taejun20/QuadStretcher/QuadStretcher Unity/Assets/Downloaded Assets/Free medieval weapons/Textures/Arrows_Arrows_AlbedoTransparency.png

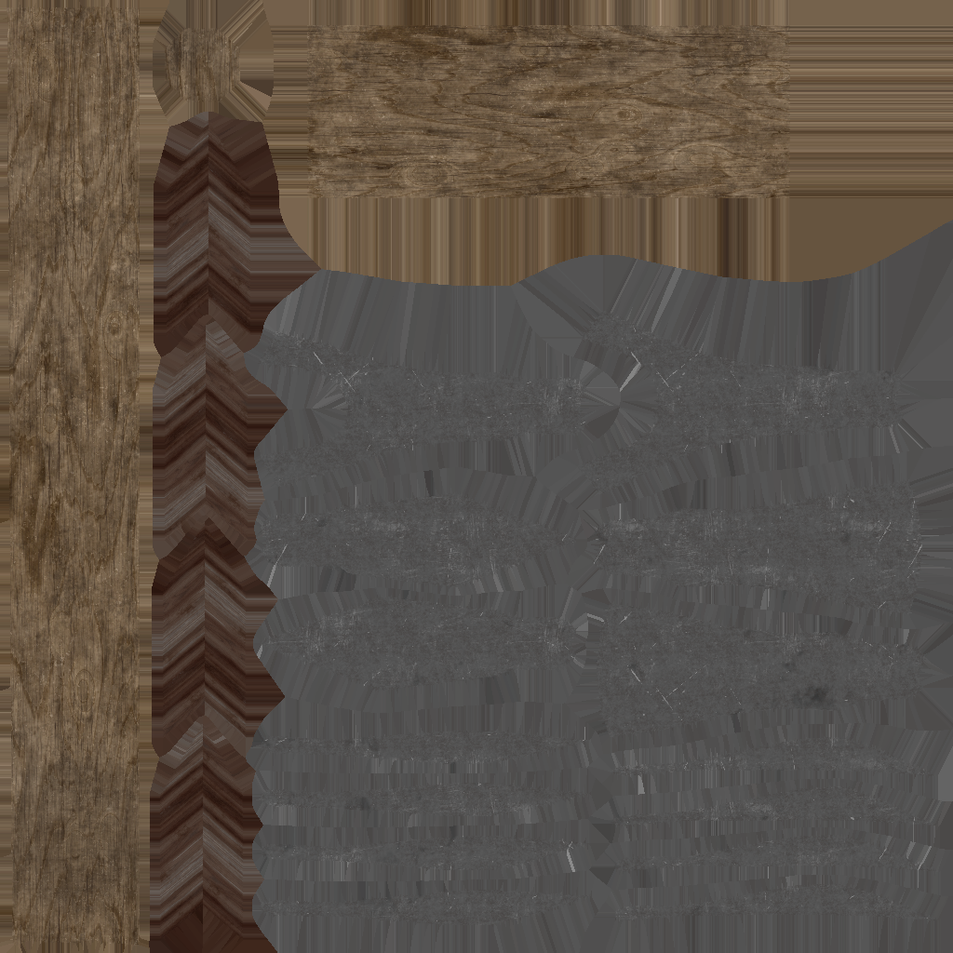
QuadStretcher Unity/Assets/Downloaded Assets/Free medieval weapons/Textures/Arrows_Arrows_AlbedoTransparency.png
