taejun20/QuadStretcher/QuadStretcher Unity/Assets/Downloaded Assets/Free medieval weapons/Textures/OneSided_Axes_low_Axes_OS_AO.png

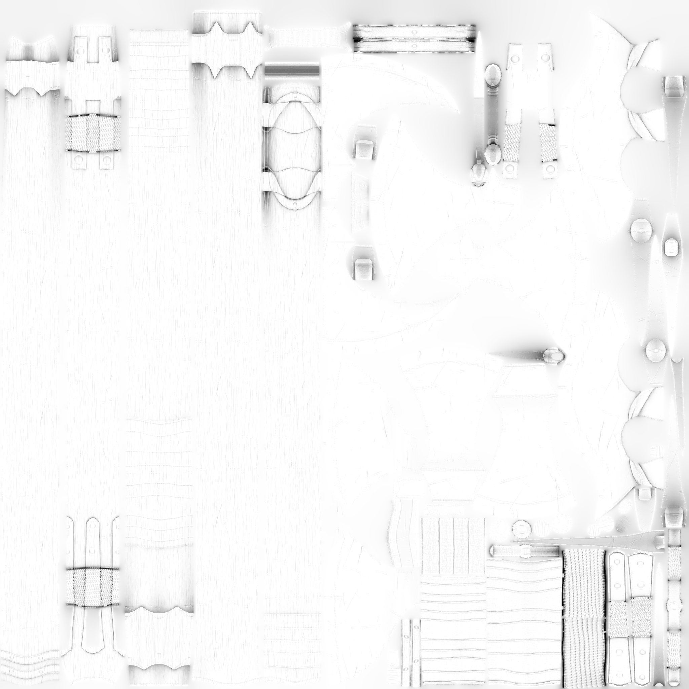
QuadStretcher Unity/Assets/Downloaded Assets/Free medieval weapons/Textures/OneSided_Axes_low_Axes_OS_AO.png
