taejun20/QuadStretcher/QuadStretcher Unity/Assets/Downloaded Assets/Free medieval weapons/Textures/Swords_low_Swords_OH_AO.png

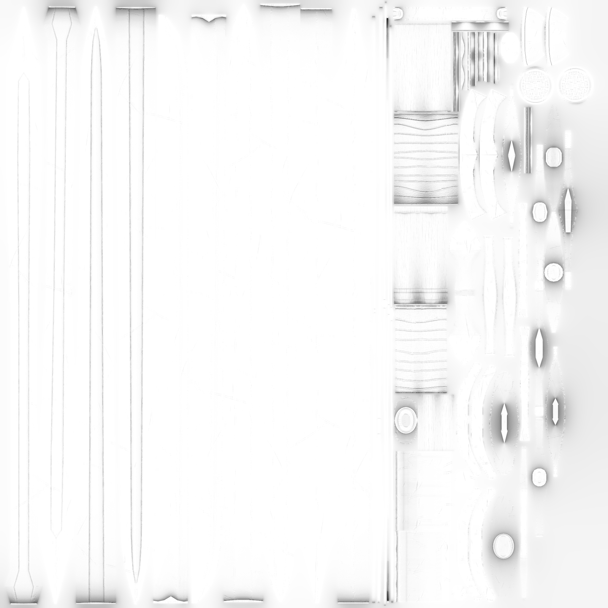
QuadStretcher Unity/Assets/Downloaded Assets/Free medieval weapons/Textures/Swords_low_Swords_OH_AO.png
