taejun20/QuadStretcher/QuadStretcher Unity/Assets/Downloaded Assets/Mega Fantasy Props Pack/Textures/bark_1_o.png

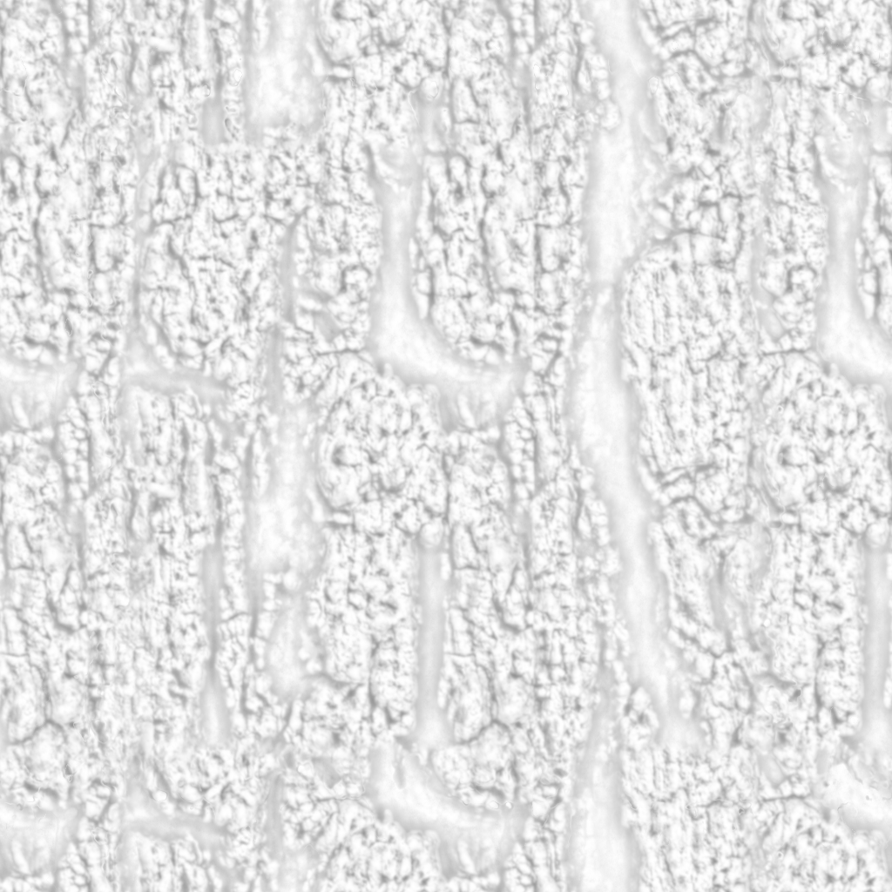
QuadStretcher Unity/Assets/Downloaded Assets/Mega Fantasy Props Pack/Textures/bark_1_o.png
