taejun20/QuadStretcher/QuadStretcher Unity/Assets/Downloaded Assets/Mega Fantasy Props Pack/Textures/books_paper_n.png

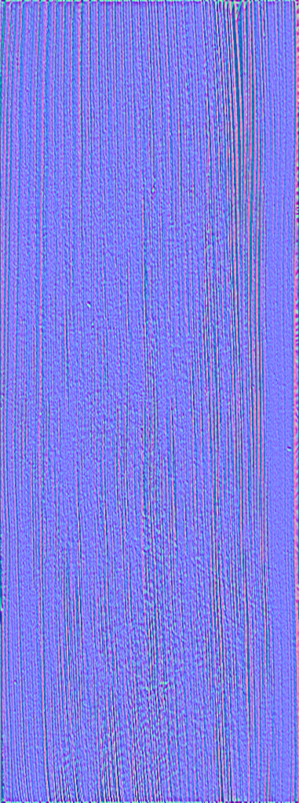
QuadStretcher Unity/Assets/Downloaded Assets/Mega Fantasy Props Pack/Textures/books_paper_n.png
