taejun20/QuadStretcher/QuadStretcher Unity/Assets/Downloaded Assets/Mega Fantasy Props Pack/Textures/books_paper_o.png

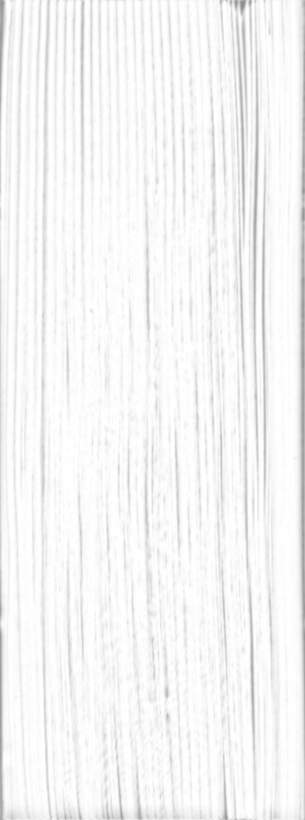
QuadStretcher Unity/Assets/Downloaded Assets/Mega Fantasy Props Pack/Textures/books_paper_o.png
