taejun20/QuadStretcher/QuadStretcher Unity/Assets/Downloaded Assets/Pistol 92/Textures/Pistol Bullet Metallic.png

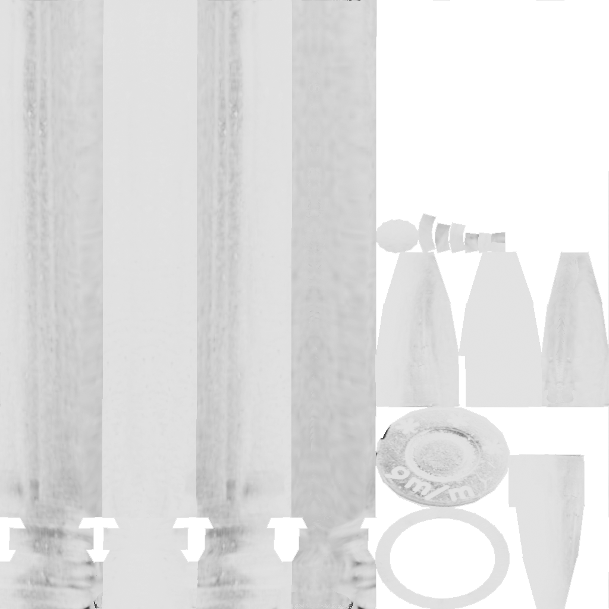
QuadStretcher Unity/Assets/Downloaded Assets/Pistol 92/Textures/Pistol Bullet Metallic.png
