taejun20/QuadStretcher/QuadStretcher Unity/Assets/Downloaded Assets/Pistol 92/Textures/Pistol Height.png

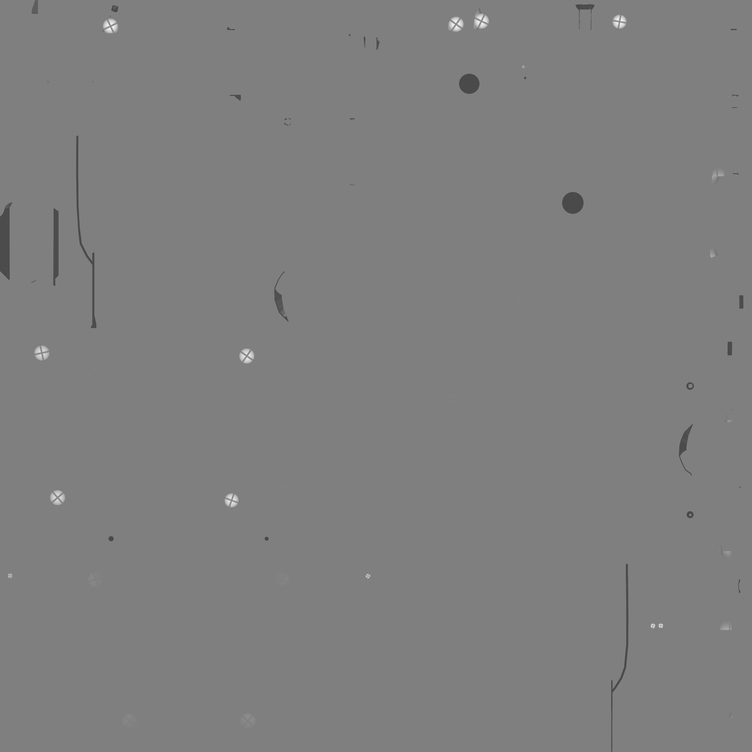
QuadStretcher Unity/Assets/Downloaded Assets/Pistol 92/Textures/Pistol Height.png
