taejun20/QuadStretcher/QuadStretcher Unity/Assets/Downloaded Assets/Platform_Pack/Pack_02_P/Texture/Folhagem_Pack_01__V2_Normal.png

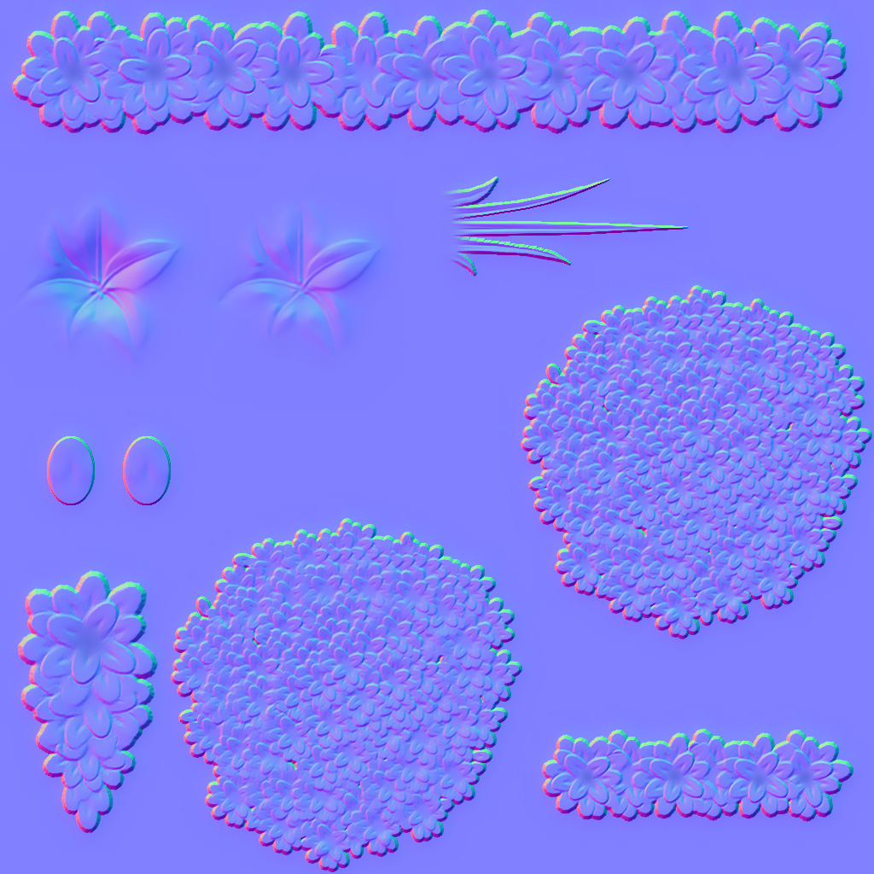
QuadStretcher Unity/Assets/Downloaded Assets/Platform_Pack/Pack_02_P/Texture/Folhagem_Pack_01__V2_Normal.png
