taejun20/QuadStretcher/QuadStretcher Unity/Assets/Downloaded Assets/Platform_Pack/S-EXTRA/Sky_01.png

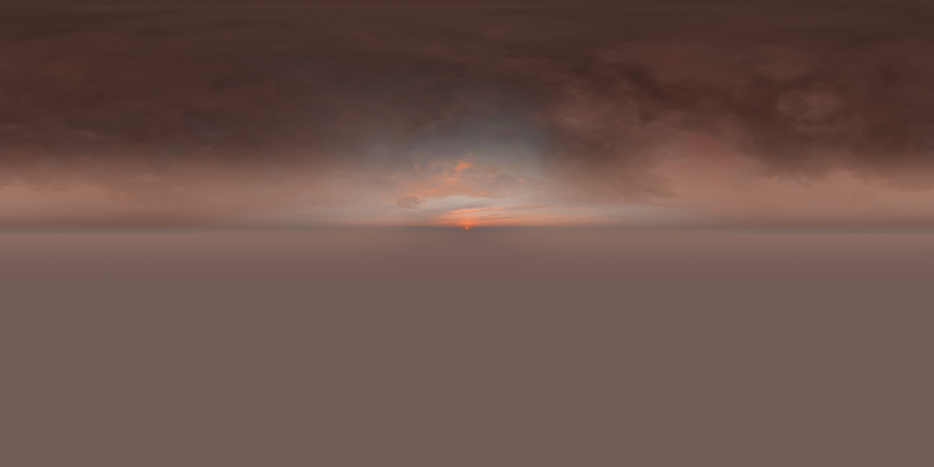
QuadStretcher Unity/Assets/Downloaded Assets/Platform_Pack/S-EXTRA/Sky_01.png
