taejun20/QuadStretcher/QuadStretcher Unity/Assets/Downloaded Assets/RPG_FPS_game_assets_industrial/Particles/Dust/Dust_v1/Source/Dust_v1.png

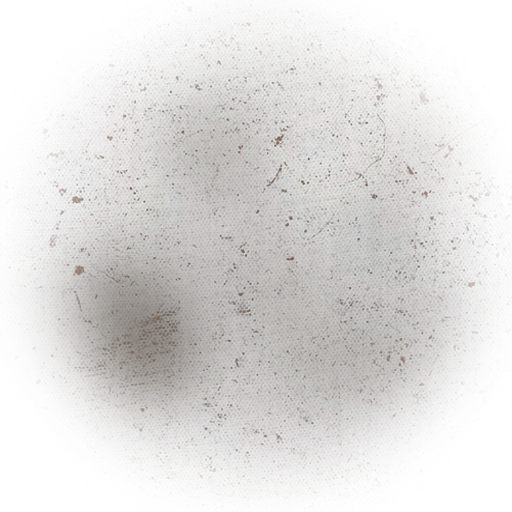
QuadStretcher Unity/Assets/Downloaded Assets/RPG_FPS_game_assets_industrial/Particles/Dust/Dust_v1/Source/Dust_v1.png
