taejun20/QuadStretcher/QuadStretcher Unity/Assets/Downloaded Assets/RPG_FPS_game_assets_industrial/Particles/Smoke/Smoke_v1/Source/Smoke_v1.png

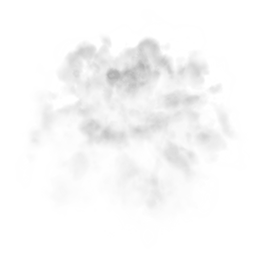
QuadStretcher Unity/Assets/Downloaded Assets/RPG_FPS_game_assets_industrial/Particles/Smoke/Smoke_v1/Source/Smoke_v1.png
