taejun20/QuadStretcher/QuadStretcher Unity/Assets/Downloaded Assets/Supercyan Free Forest Sample/Textures/Foliage/forestpack_foliage_diffuse.png

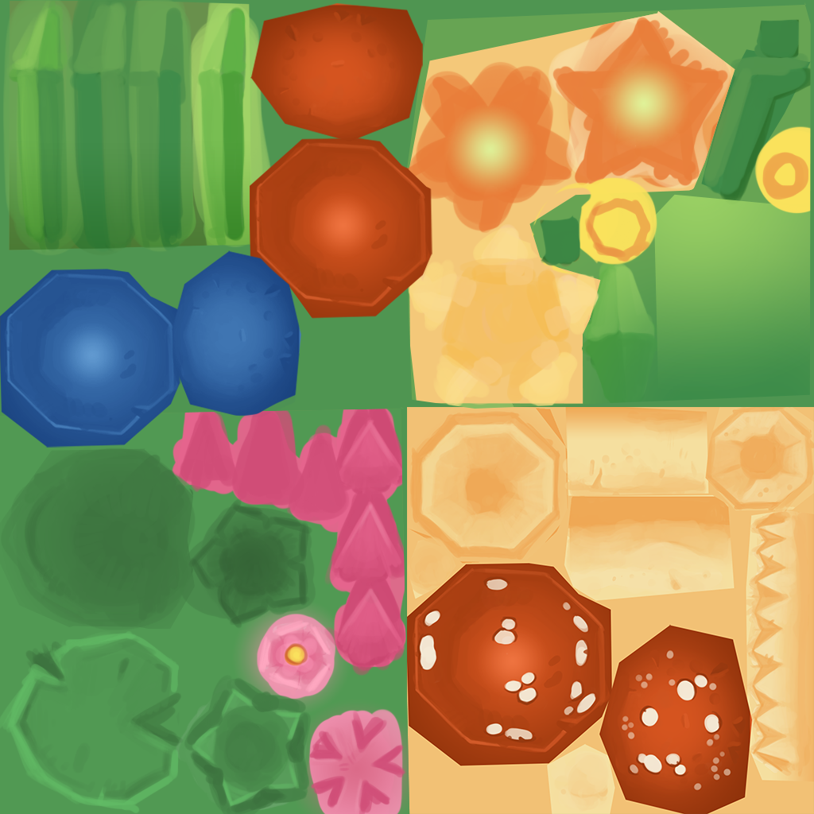
QuadStretcher Unity/Assets/Downloaded Assets/Supercyan Free Forest Sample/Textures/Foliage/forestpack_foliage_diffuse.png
