taejun20/QuadStretcher/QuadStretcher Unity/Assets/Downloaded Assets/Supercyan Free Forest Sample/Textures/Ground/forestpack_road_tile_diffuse.png

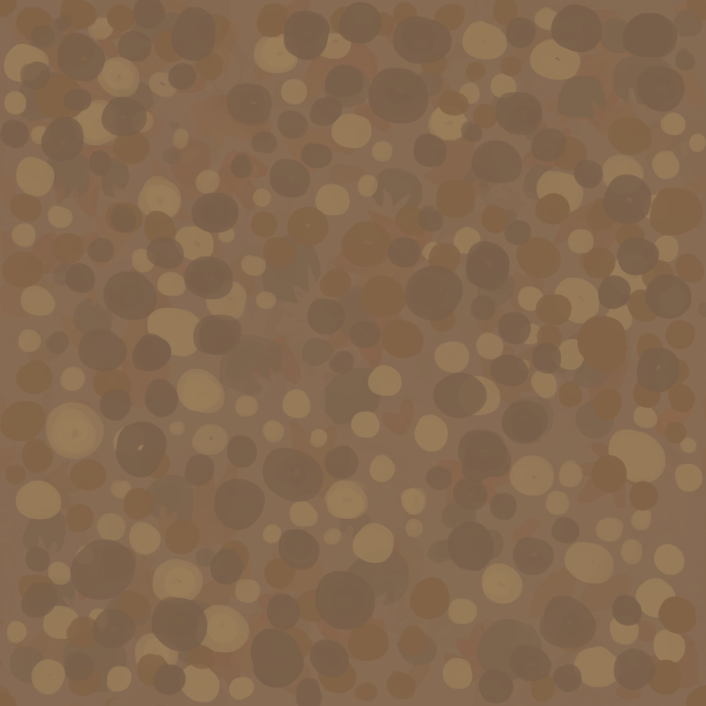
QuadStretcher Unity/Assets/Downloaded Assets/Supercyan Free Forest Sample/Textures/Ground/forestpack_road_tile_diffuse.png
