taejun20/QuadStretcher/QuadStretcher Unity/Assets/Downloaded Assets/Supercyan Free Forest Sample/Textures/Skybox/ny.png

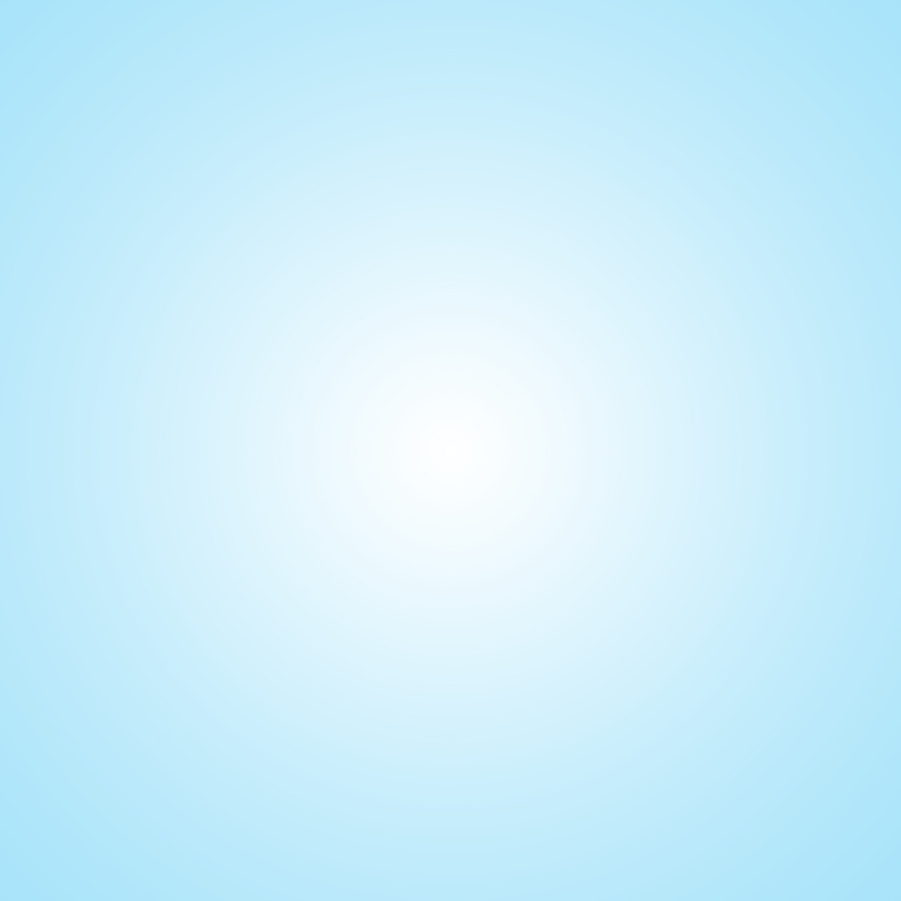
QuadStretcher Unity/Assets/Downloaded Assets/Supercyan Free Forest Sample/Textures/Skybox/ny.png
