taejun20/QuadStretcher/QuadStretcher Unity/Assets/Downloaded Assets/Supercyan Free Forest Sample/Textures/Skybox/nz.png

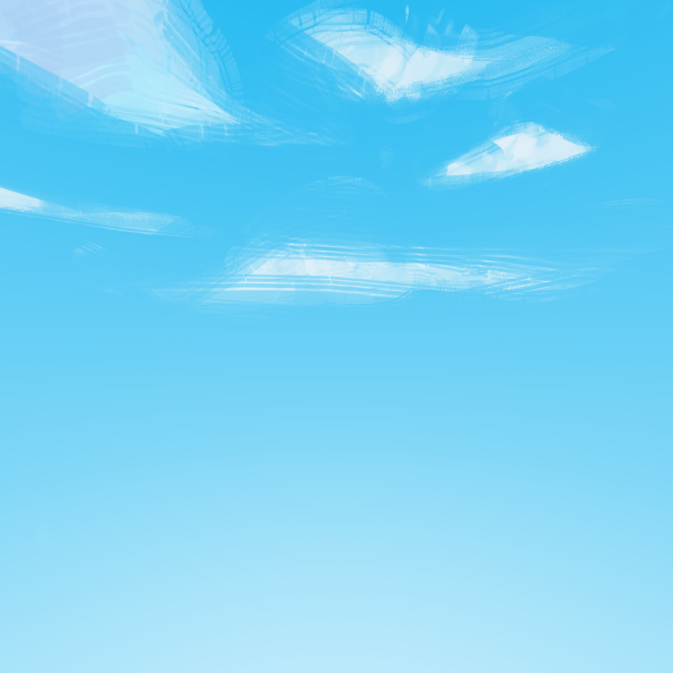
QuadStretcher Unity/Assets/Downloaded Assets/Supercyan Free Forest Sample/Textures/Skybox/nz.png
