taejun20/QuadStretcher/QuadStretcher Unity/Assets/Downloaded Assets/Water Shaders V2/Example Scenes/Environment/Particles/Particle.png

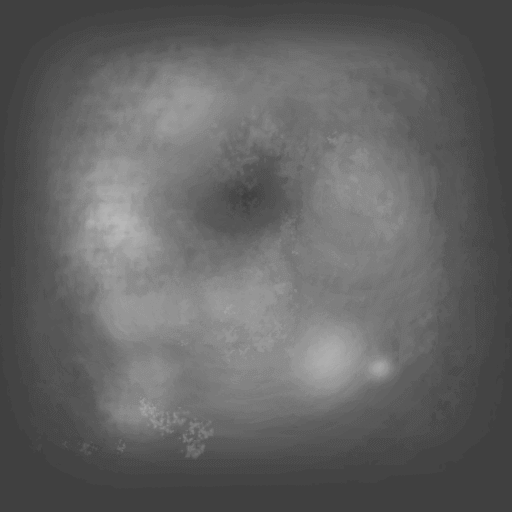
QuadStretcher Unity/Assets/Downloaded Assets/Water Shaders V2/Example Scenes/Environment/Particles/Particle.png
