taejun20/QuadStretcher/QuadStretcher Unity/Assets/Downloaded Assets/Water Shaders V2/Example Scenes/PostProcessing/Utilities/CustomMotionTexture/Textures/WheelMotionVectors.png

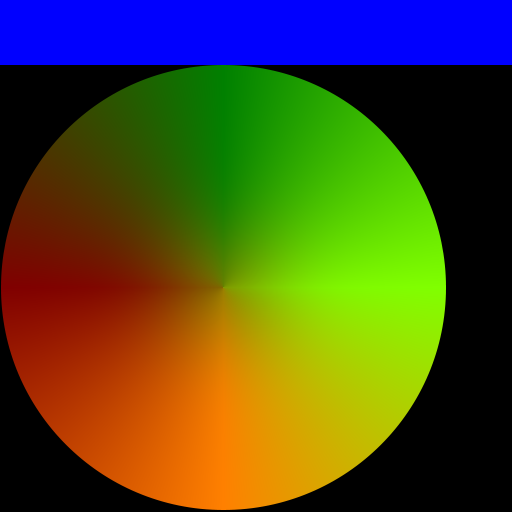
QuadStretcher Unity/Assets/Downloaded Assets/Water Shaders V2/Example Scenes/PostProcessing/Utilities/CustomMotionTexture/Textures/WheelMotionVectors.png
