taejun20/QuadStretcher/QuadStretcher Unity/Assets/Downloaded Assets/Weapon box/Texture/Weapon box_occlusion.png

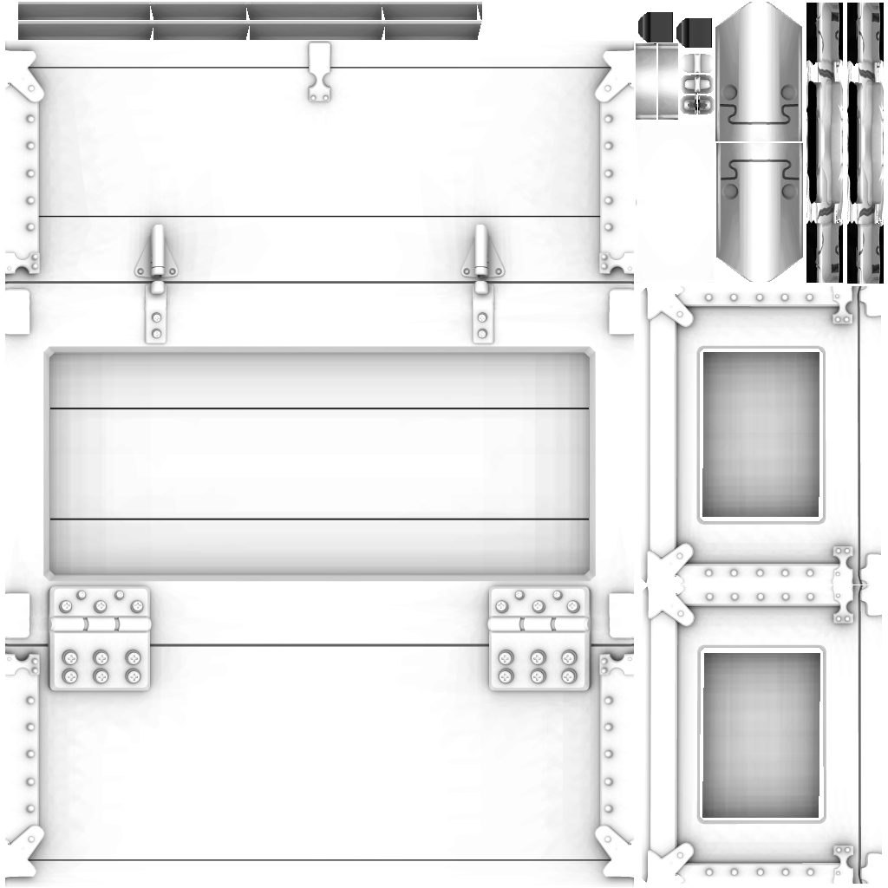
QuadStretcher Unity/Assets/Downloaded Assets/Weapon box/Texture/Weapon box_occlusion.png
