taejun20/QuadStretcher/QuadStretcher Unity/Assets/Oculus/LipSync/Models/FemaleHead_Morph/skin_DIFF.png

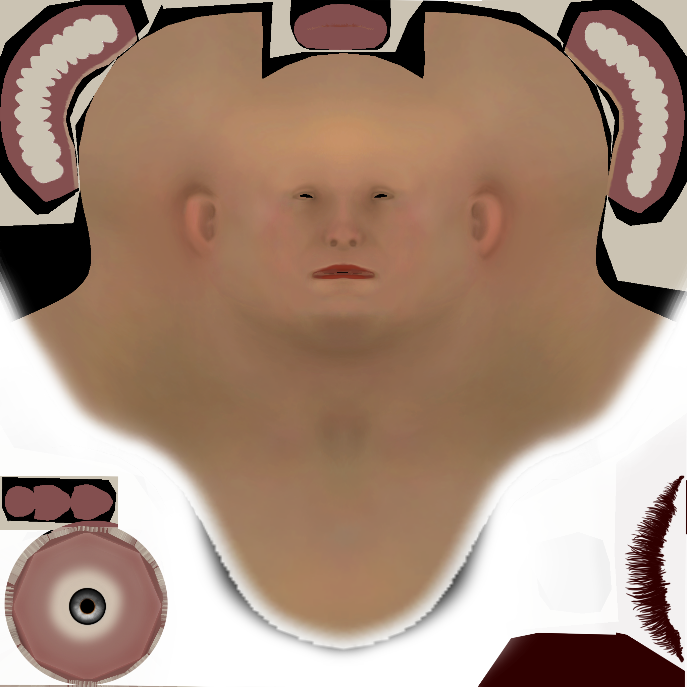
QuadStretcher Unity/Assets/Oculus/LipSync/Models/FemaleHead_Morph/skin_DIFF.png
