taejun20/QuadStretcher/QuadStretcher Unity/Assets/Oculus/LipSync/Models/RobotHead_TextureFlip/CH.png

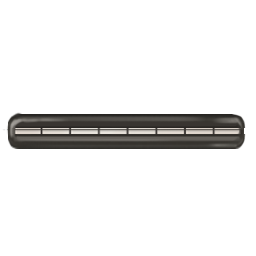
QuadStretcher Unity/Assets/Oculus/LipSync/Models/RobotHead_TextureFlip/CH.png
