taejun20/QuadStretcher/QuadStretcher Unity/Assets/Oculus/LipSync/Models/RobotHead_TextureFlip/DD.png

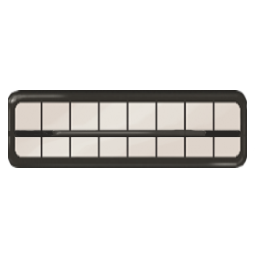
QuadStretcher Unity/Assets/Oculus/LipSync/Models/RobotHead_TextureFlip/DD.png
