taejun20/QuadStretcher/QuadStretcher Unity/Assets/Oculus/LipSync/Models/RobotHead_TextureFlip/E.png

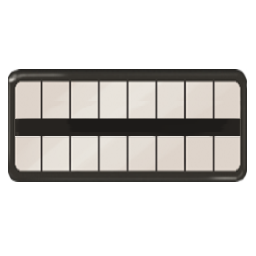
QuadStretcher Unity/Assets/Oculus/LipSync/Models/RobotHead_TextureFlip/E.png
