taejun20/QuadStretcher/QuadStretcher Unity/Assets/Oculus/LipSync/Models/RobotHead_TextureFlip/FF.png

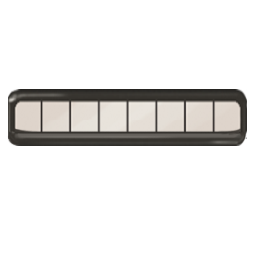
QuadStretcher Unity/Assets/Oculus/LipSync/Models/RobotHead_TextureFlip/FF.png
