taejun20/QuadStretcher/QuadStretcher Unity/Assets/Oculus/SampleFramework/Core/CustomHands/Textures/noise_01.png

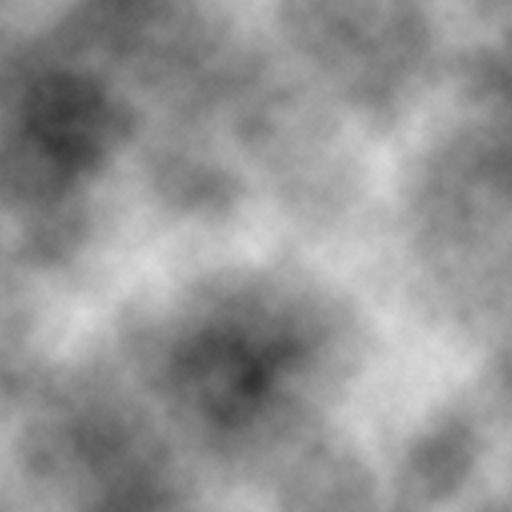
QuadStretcher Unity/Assets/Oculus/SampleFramework/Core/CustomHands/Textures/noise_01.png
