taejun20/QuadStretcher/QuadStretcher Unity/Assets/Oculus/SampleFramework/Core/CustomHands/Textures/ramp_bluewhite_01.png

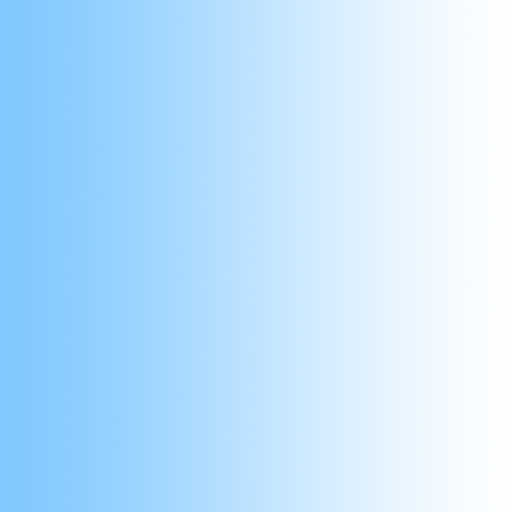
QuadStretcher Unity/Assets/Oculus/SampleFramework/Core/CustomHands/Textures/ramp_bluewhite_01.png
