taejun20/QuadStretcher/QuadStretcher Unity/Assets/Oculus/VR/Textures/gaze_cursor.png

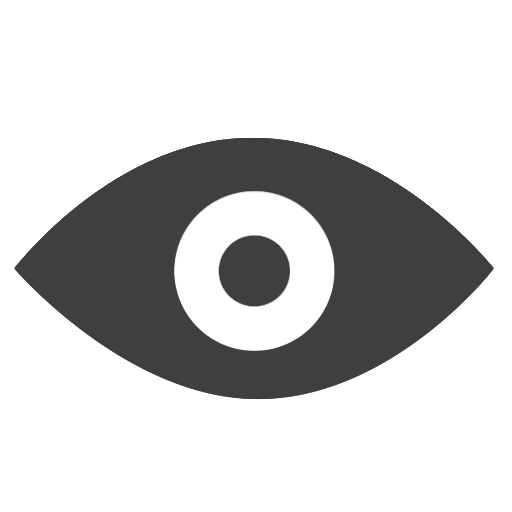
QuadStretcher Unity/Assets/Oculus/VR/Textures/gaze_cursor.png
