taejun20/QuadStretcher/QuadStretcher Unity/Assets/Oculus/VR/Textures/HandTracking/HandTracking_uvmap_2048.png

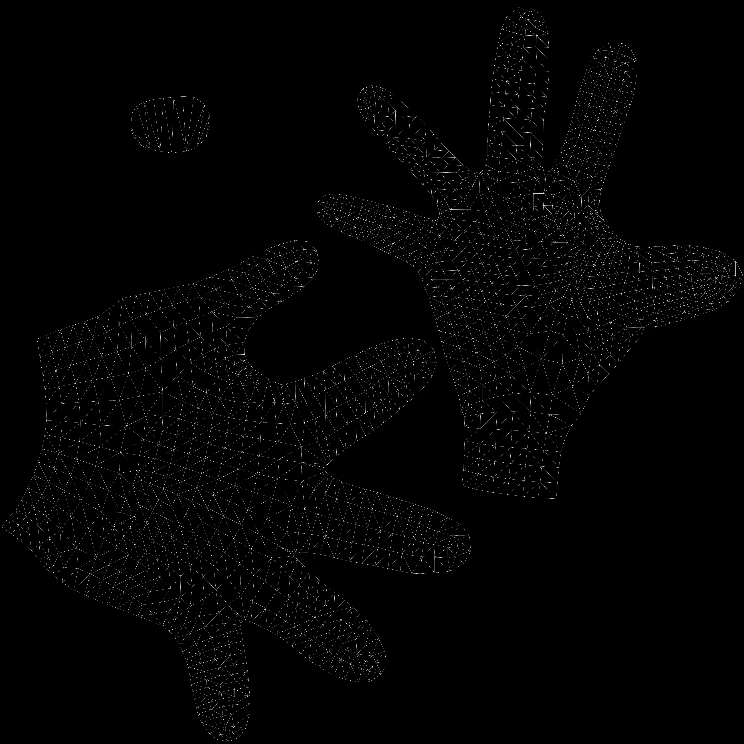
QuadStretcher Unity/Assets/Oculus/VR/Textures/HandTracking/HandTracking_uvmap_2048.png
