taejun20/QuadStretcher/QuadStretcher Unity/Assets/Oculus/VR/Textures/windowgui.png

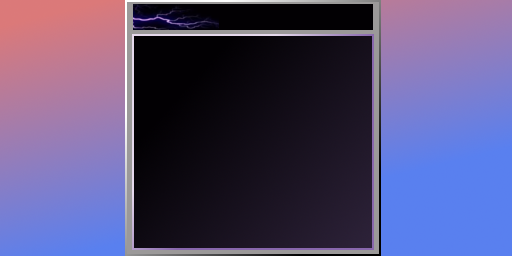
QuadStretcher Unity/Assets/Oculus/VR/Textures/windowgui.png
