taejun20/QuadStretcher/QuadStretcher Unity/Assets/Downloaded Assets/Water Shaders V2/Example Scenes/Environment/#NVJOB Assets/Dynamic Sky (For Demo)/Materials/Clouds A1.png

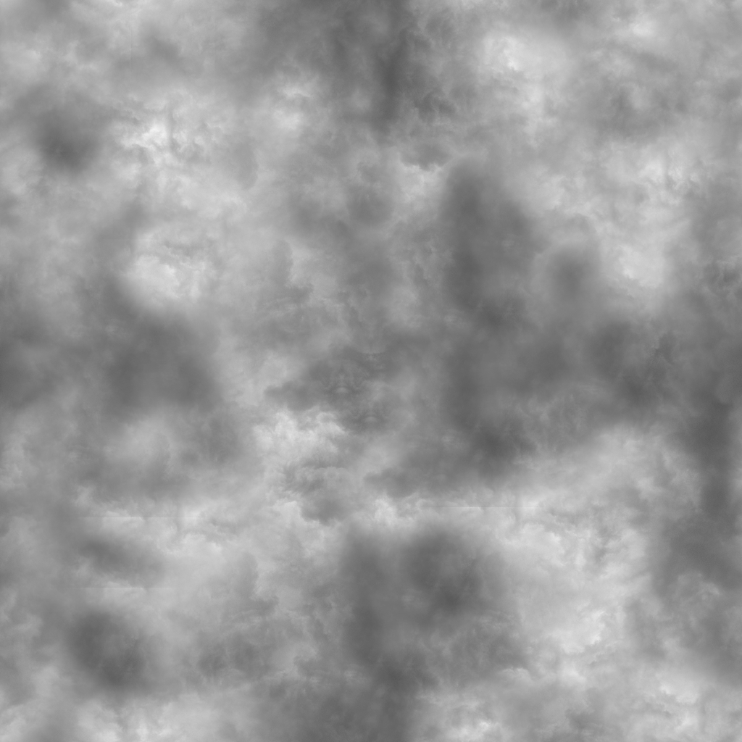
QuadStretcher Unity/Assets/Downloaded Assets/Water Shaders V2/Example Scenes/Environment/#NVJOB Assets/Dynamic Sky (For Demo)/Materials/Clouds A1.png
