taejun20/QuadStretcher/QuadStretcher Unity/Assets/Downloaded Assets/Water Shaders V2/Examples Water/Materials/Textures/Water A 0.png

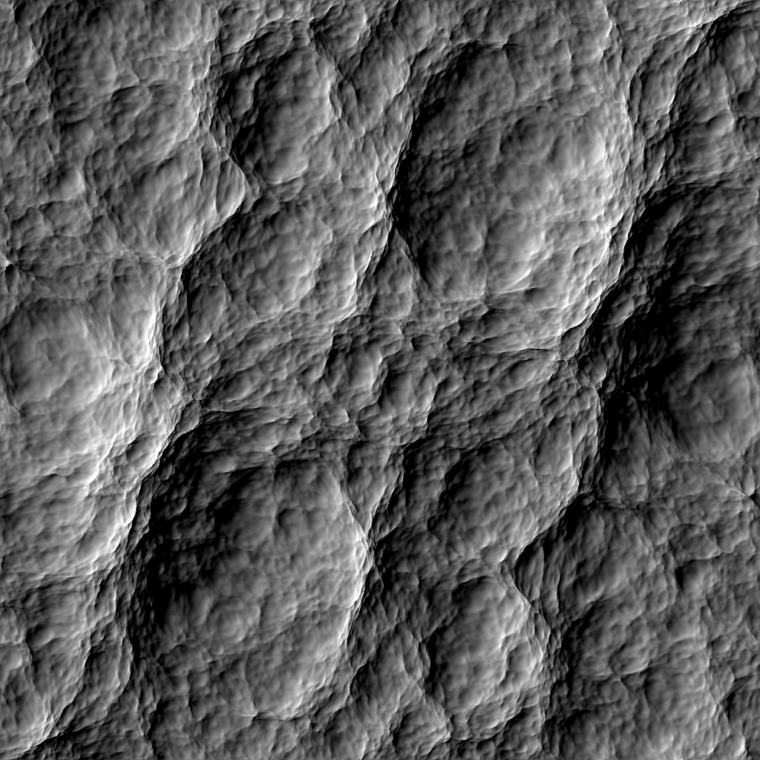
QuadStretcher Unity/Assets/Downloaded Assets/Water Shaders V2/Examples Water/Materials/Textures/Water A 0.png
