taejun20/QuadStretcher/QuadStretcher Unity/Assets/Materials/SlingshotScene/Target.png

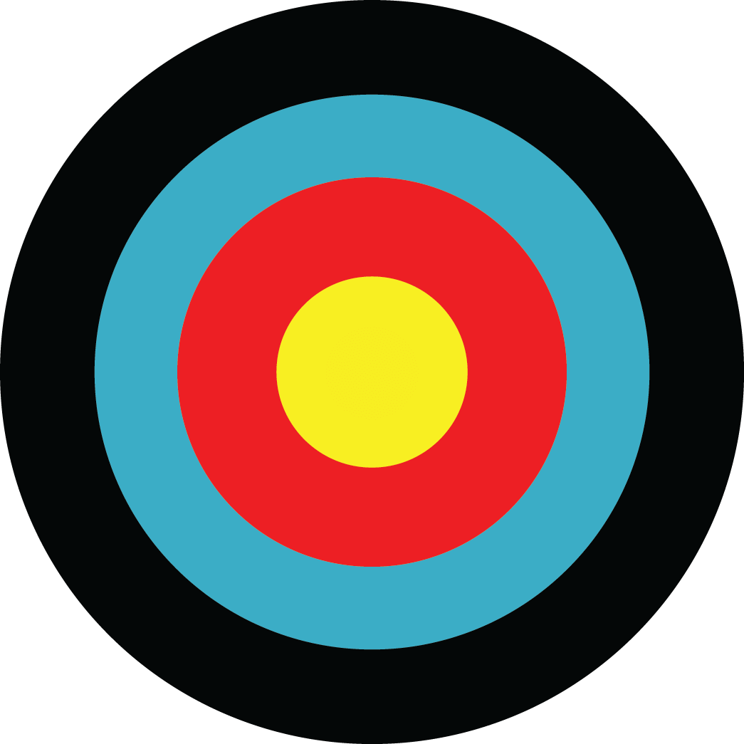
QuadStretcher Unity/Assets/Materials/SlingshotScene/Target.png
