taejun20/QuadStretcher/QuadStretcher Unity/Assets/Oculus/SampleFramework/Core/Locomotion/Materials/MeterGrid.png

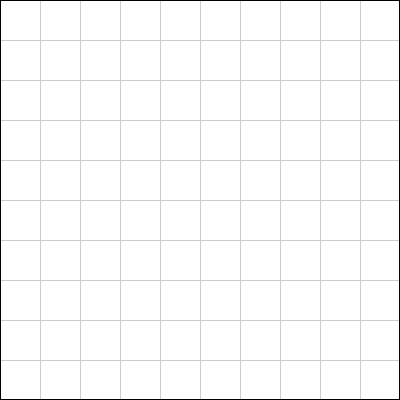
QuadStretcher Unity/Assets/Oculus/SampleFramework/Core/Locomotion/Materials/MeterGrid.png
