taejun20/QuadStretcher/QuadStretcher Unity/Assets/Oculus/SampleFramework/Core/TouchControllers/Materials/Textures/touchController_albedo.png

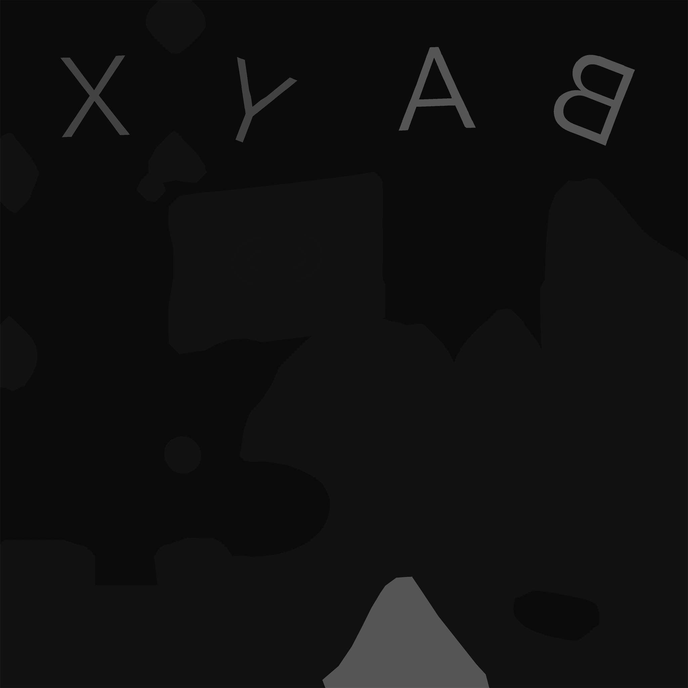
QuadStretcher Unity/Assets/Oculus/SampleFramework/Core/TouchControllers/Materials/Textures/touchController_albedo.png
