taejun20/QuadStretcher/QuadStretcher Unity/Assets/Oculus/SampleFramework/Usage/DistanceGrab/Materials/triangles.png

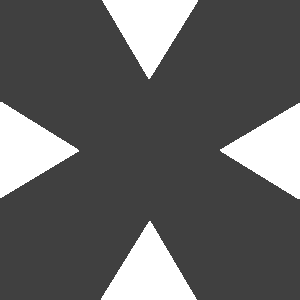
QuadStretcher Unity/Assets/Oculus/SampleFramework/Usage/DistanceGrab/Materials/triangles.png
