taejun20/QuadStretcher/QuadStretcher Unity/Assets/Oculus/SampleFramework/Usage/CustomHands/Lightmap-0_comp_dir.png

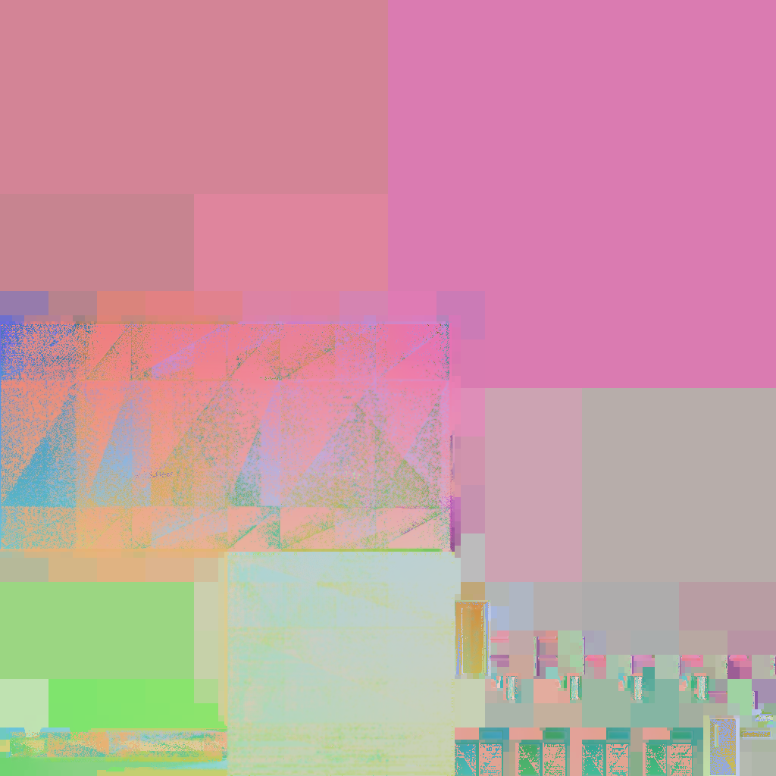
QuadStretcher Unity/Assets/Oculus/SampleFramework/Usage/CustomHands/Lightmap-0_comp_dir.png
