taejun20/QuadStretcher/QuadStretcher Unity/Assets/Oculus/SampleFramework/Usage/HandsTrainExample/Textures/HandsNotification.png

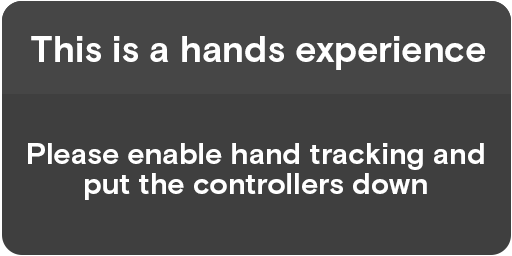
QuadStretcher Unity/Assets/Oculus/SampleFramework/Usage/HandsTrainExample/Textures/HandsNotification.png
