taejun20/QuadStretcher/QuadStretcher Unity/Assets/Oculus/SampleFramework/Usage/Locomotion/Textures/concrete_01_msm.png

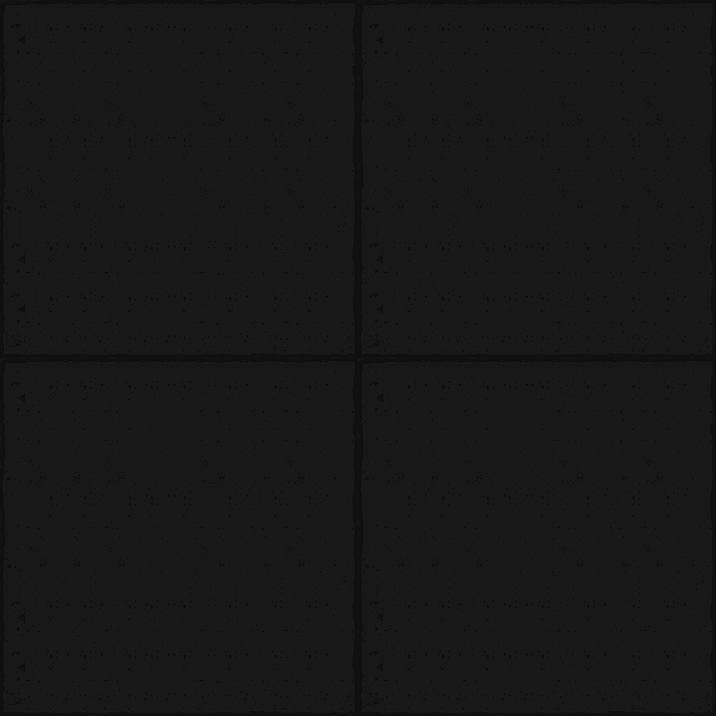
QuadStretcher Unity/Assets/Oculus/SampleFramework/Usage/Locomotion/Textures/concrete_01_msm.png
