taejun20/QuadStretcher/QuadStretcher Unity/Assets/Oculus/SampleFramework/Usage/Locomotion/Textures/floor_tile_01_amb.png

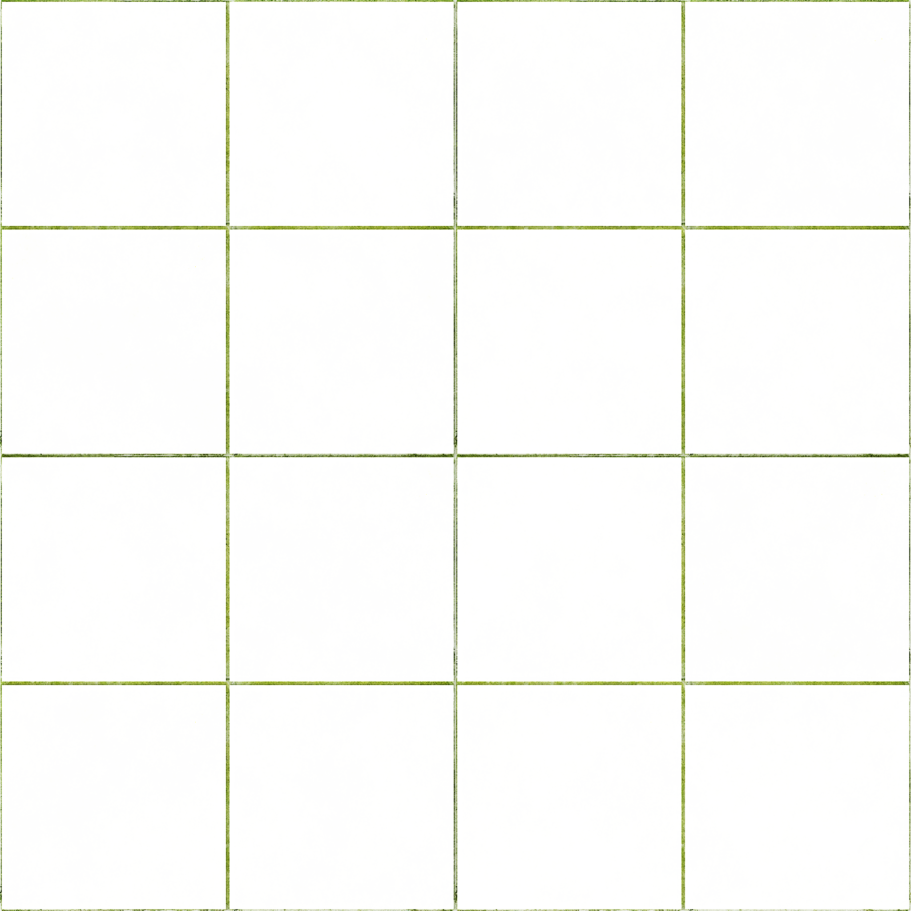
QuadStretcher Unity/Assets/Oculus/SampleFramework/Usage/Locomotion/Textures/floor_tile_01_amb.png
