taejun20/QuadStretcher/QuadStretcher Unity/Assets/Oculus/SampleFramework/Usage/Locomotion/Textures/floor_tile_01_msm.png

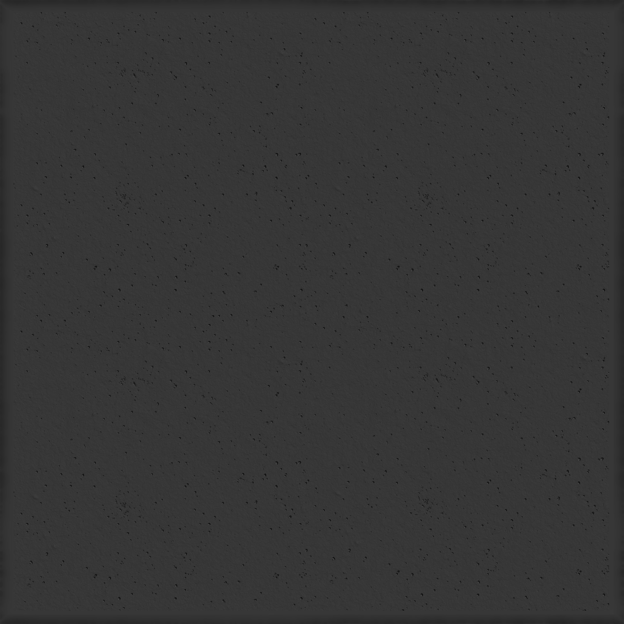
QuadStretcher Unity/Assets/Oculus/SampleFramework/Usage/Locomotion/Textures/floor_tile_01_msm.png
