taejun20/QuadStretcher/QuadStretcher Unity/Assets/Oculus/SampleFramework/Usage/Locomotion/Textures/grid_01.png

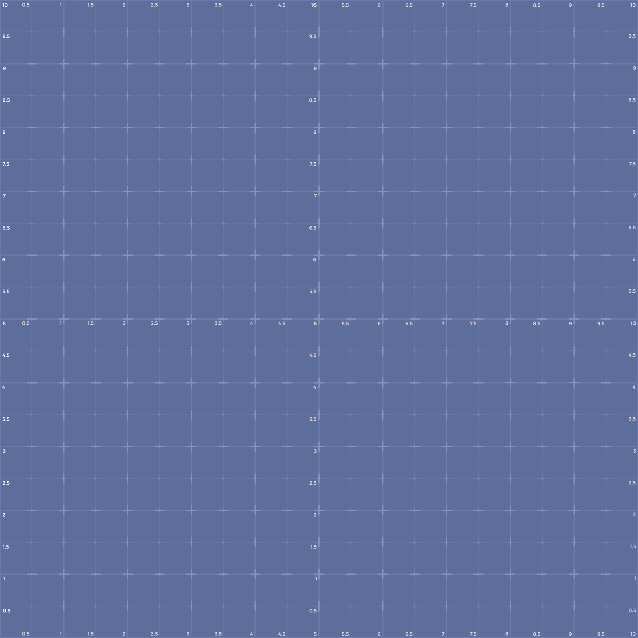
QuadStretcher Unity/Assets/Oculus/SampleFramework/Usage/Locomotion/Textures/grid_01.png
