taejun20/QuadStretcher/QuadStretcher Unity/Assets/Oculus/SampleFramework/Usage/OVROverlay/Textures/Loading.png

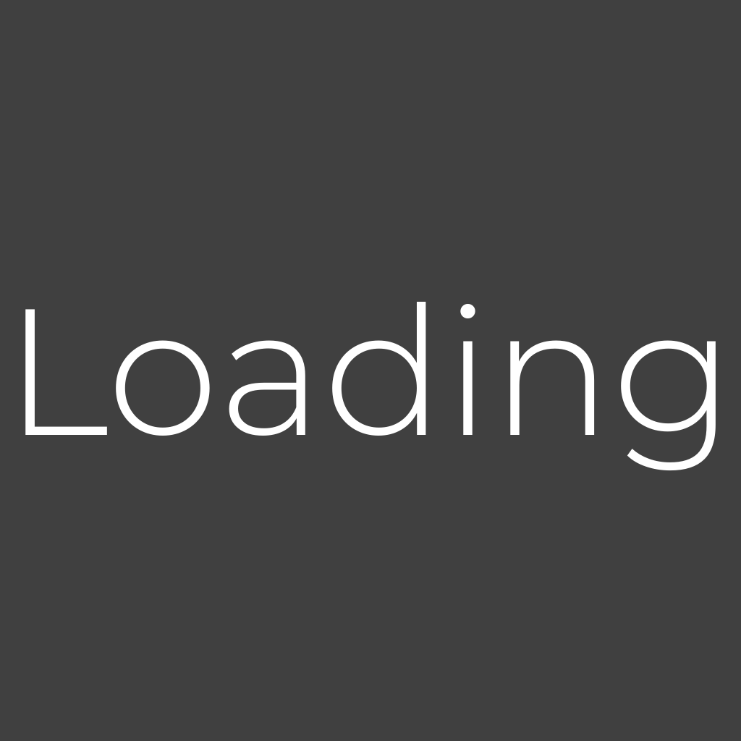
QuadStretcher Unity/Assets/Oculus/SampleFramework/Usage/OVROverlay/Textures/Loading.png
