taejun20/QuadStretcher/QuadStretcher Unity/Assets/Oculus/SampleFramework/Usage/OVROverlay/Textures/QuadOverlayText.png

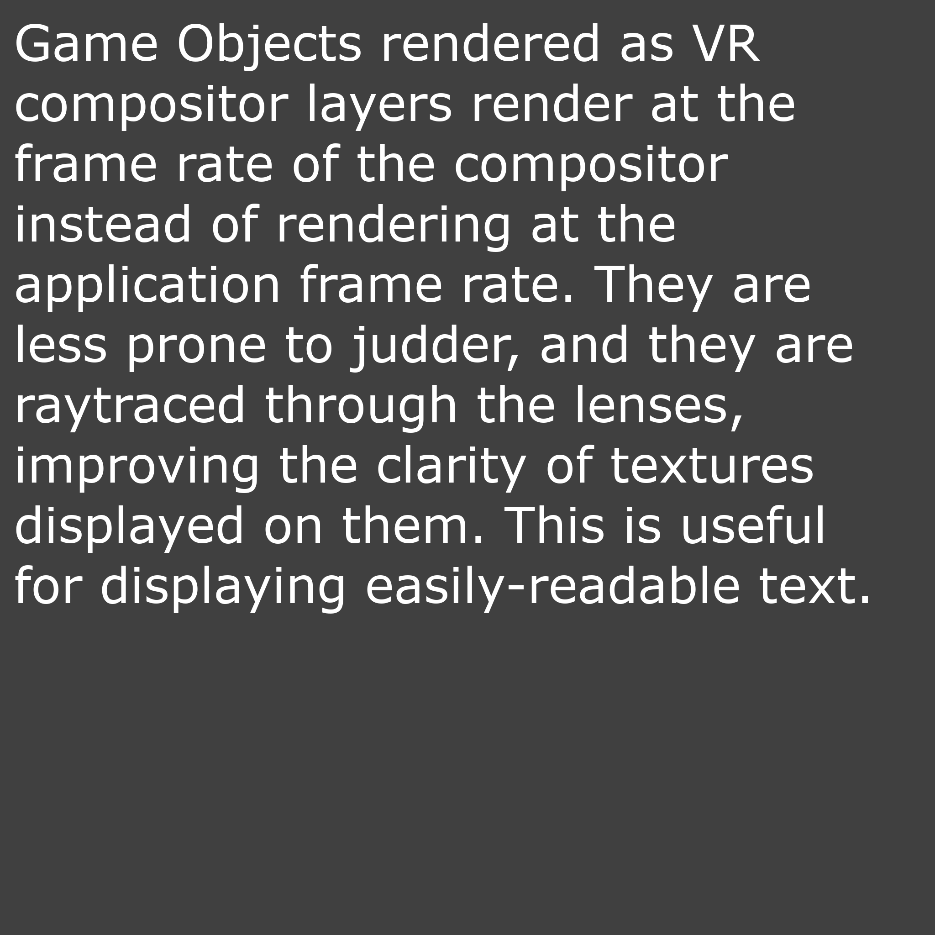
QuadStretcher Unity/Assets/Oculus/SampleFramework/Usage/OVROverlay/Textures/QuadOverlayText.png
