taejun20/QuadStretcher/QuadStretcher Unity/Assets/Oculus/SampleFramework/Usage/OVROverlay/Textures/Tile_Texture_360Photo.png

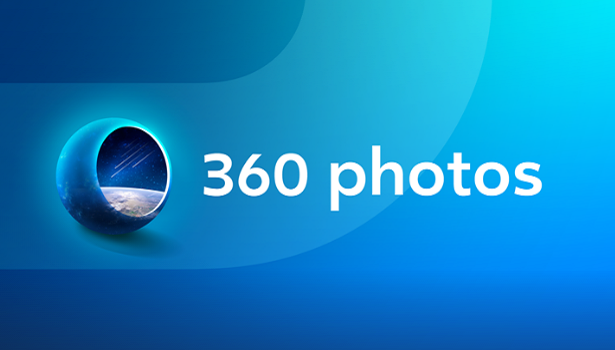
QuadStretcher Unity/Assets/Oculus/SampleFramework/Usage/OVROverlay/Textures/Tile_Texture_360Photo.png
