taejun20/QuadStretcher/QuadStretcher Unity/Assets/Oculus/SampleFramework/Usage/SharedAssets/Textures/block_wood_01_dif.png

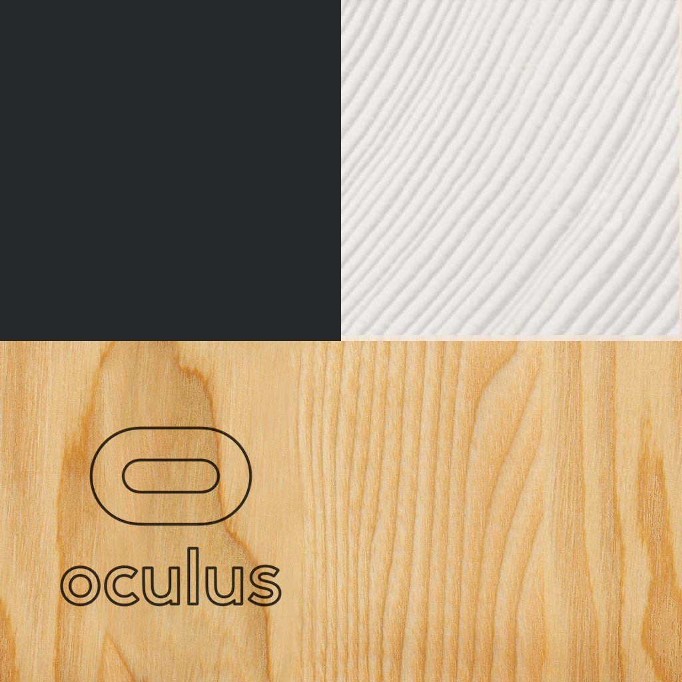
QuadStretcher Unity/Assets/Oculus/SampleFramework/Usage/SharedAssets/Textures/block_wood_01_dif.png
