taejun20/QuadStretcher/QuadStretcher Unity/Assets/Oculus/SampleFramework/Usage/SharedAssets/Textures/room_atlas_01.png

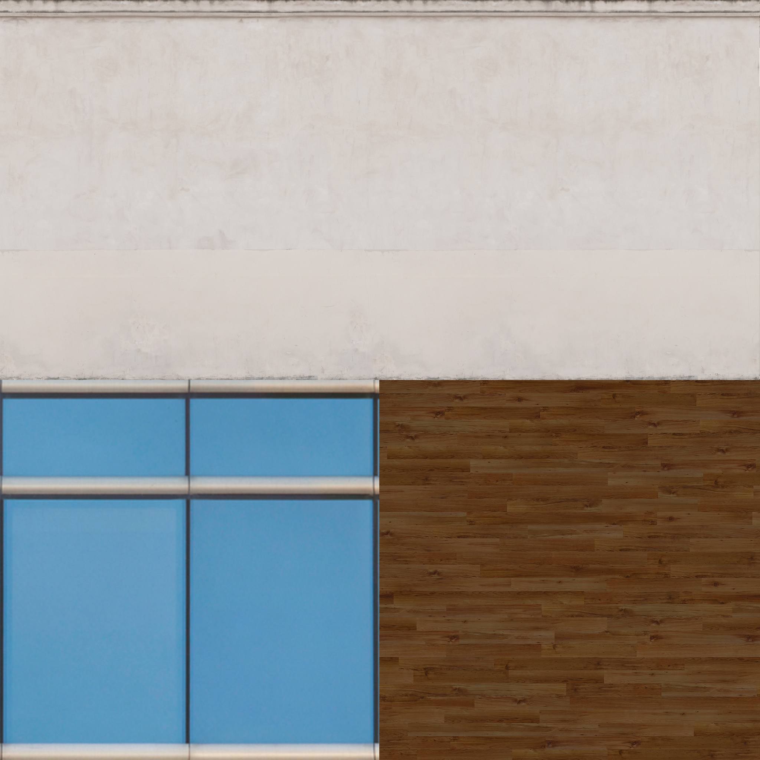
QuadStretcher Unity/Assets/Oculus/SampleFramework/Usage/SharedAssets/Textures/room_atlas_01.png
