taejun20/QuadStretcher/QuadStretcher Unity/Assets/Oculus/SampleFramework/Core/DebugUI/Textures/dialog.png

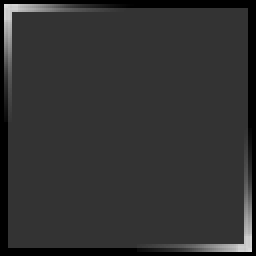
QuadStretcher Unity/Assets/Oculus/SampleFramework/Core/DebugUI/Textures/dialog.png
